Zabret/Arduino-programable-pedal-project/slike_projekt/p2.PNG

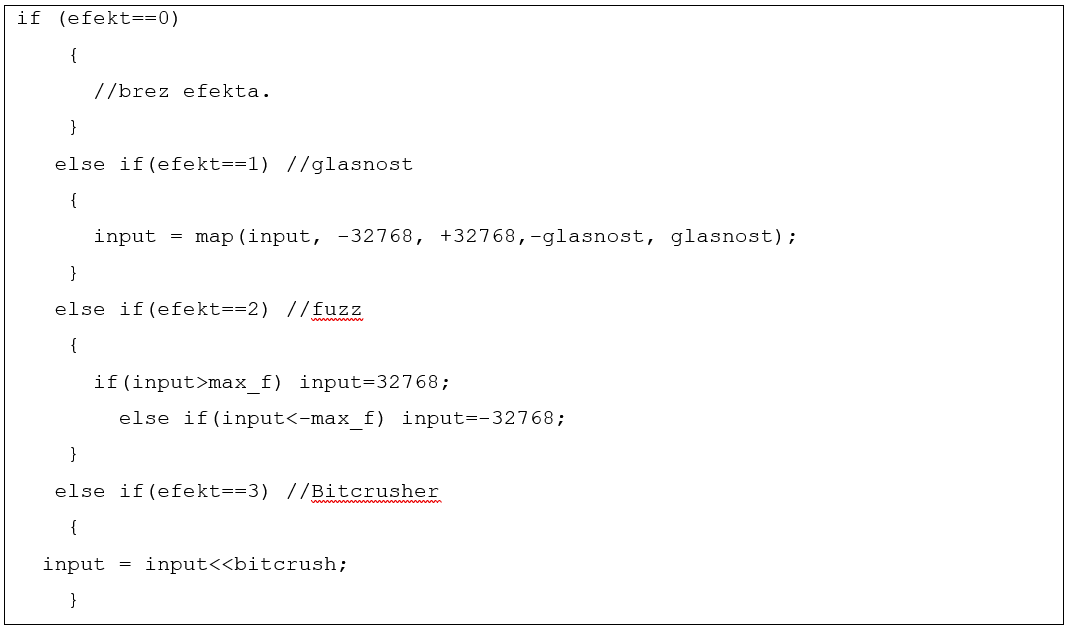
slike_projekt/p2.PNG
